aldura85/Mecanum-Autonomous-Vehicle/project_codes/python_pc_folder/Yolo_training_reslut/BoxF1_curve.png

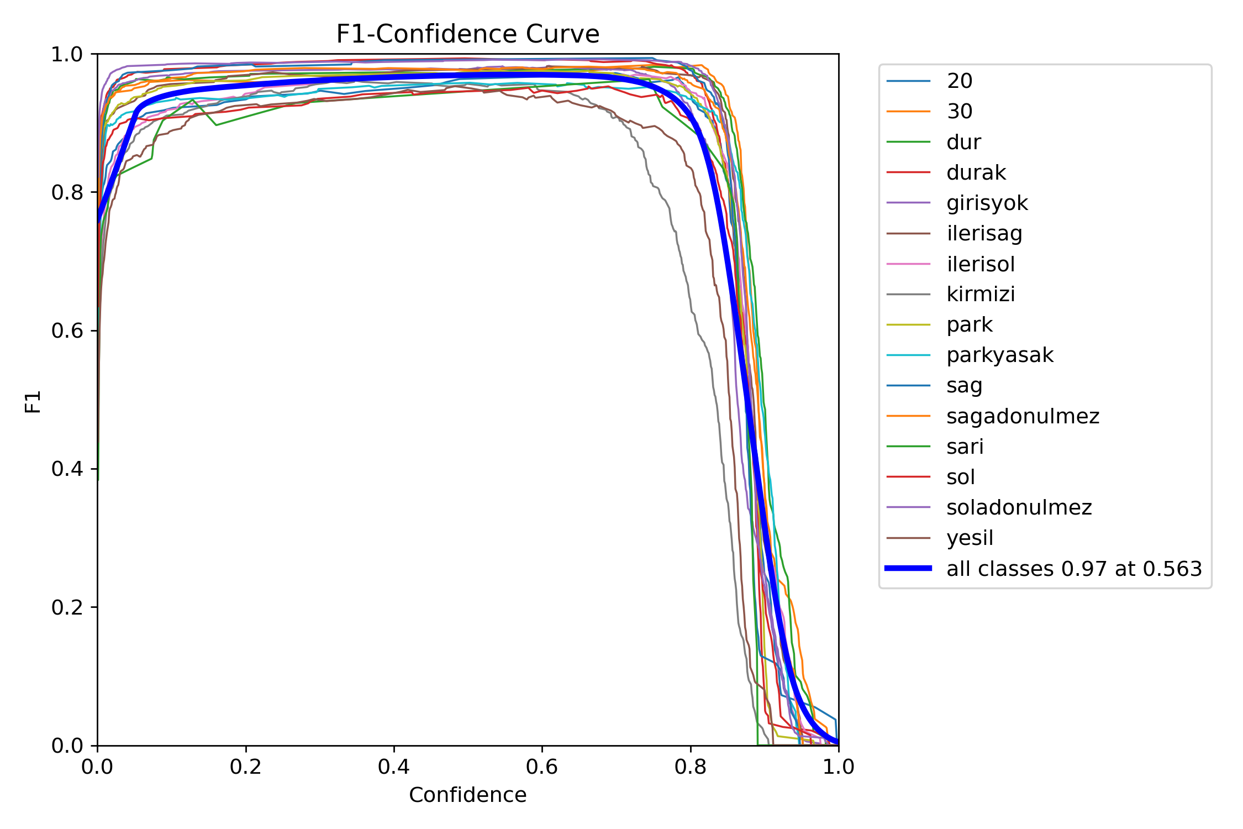
project_codes/python_pc_folder/Yolo_training_reslut/BoxF1_curve.png
