aldura85/Mecanum-Autonomous-Vehicle/project_codes/python_pc_folder/Yolo_training_reslut/confusion_matrix.png

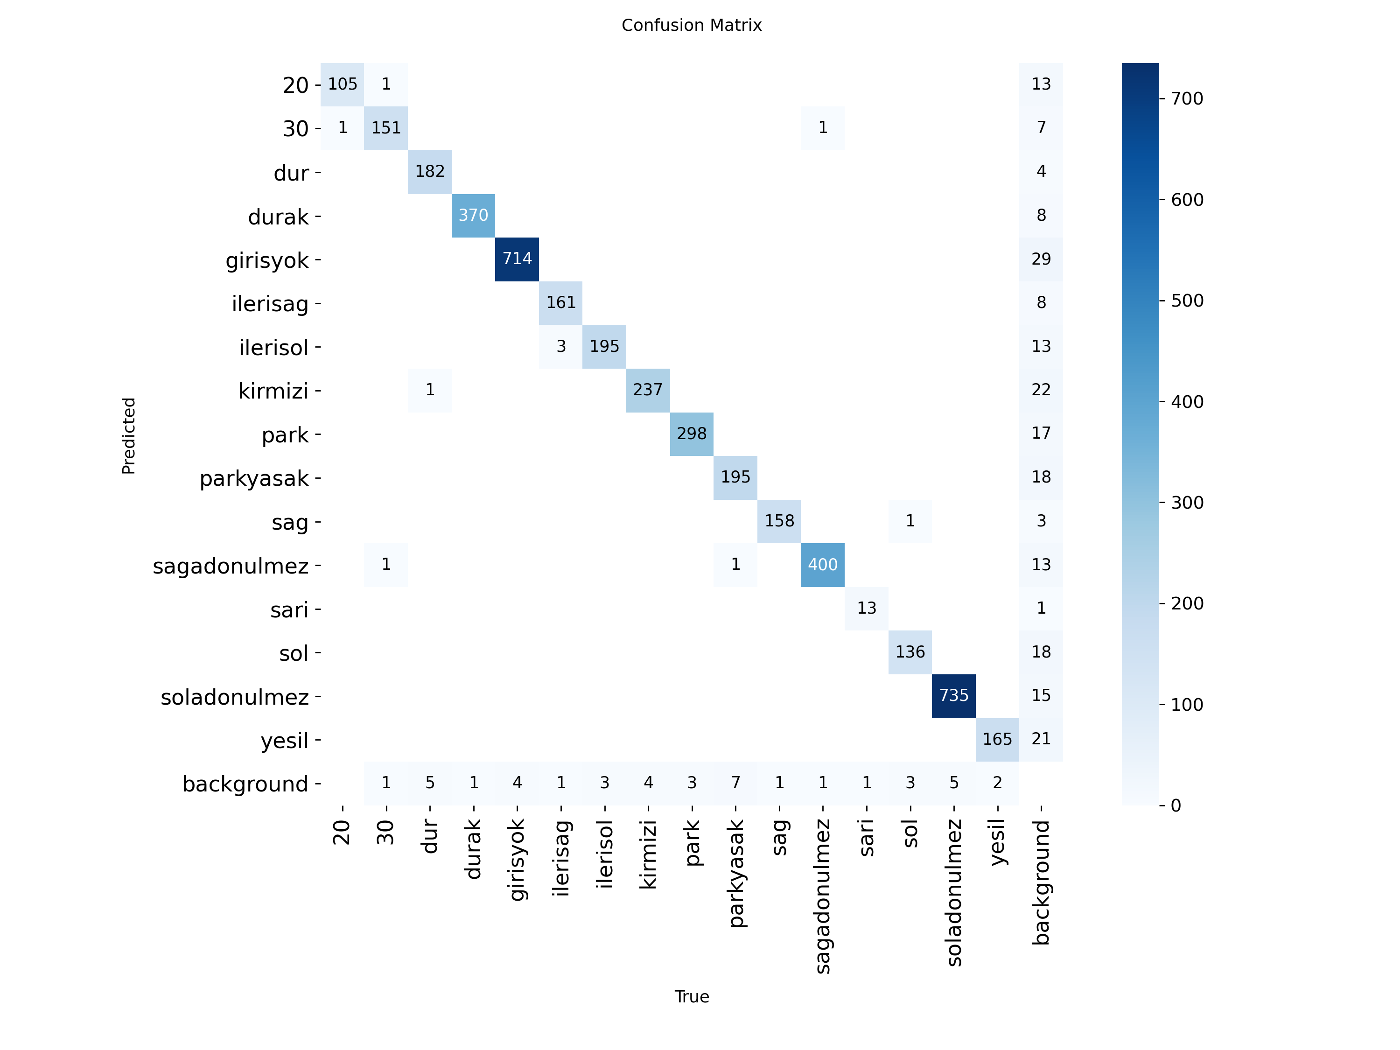
project_codes/python_pc_folder/Yolo_training_reslut/confusion_matrix.png
