aldura85/Mecanum-Autonomous-Vehicle/project_codes/python_pc_folder/Yolo_training_reslut/train_batch2.jpg

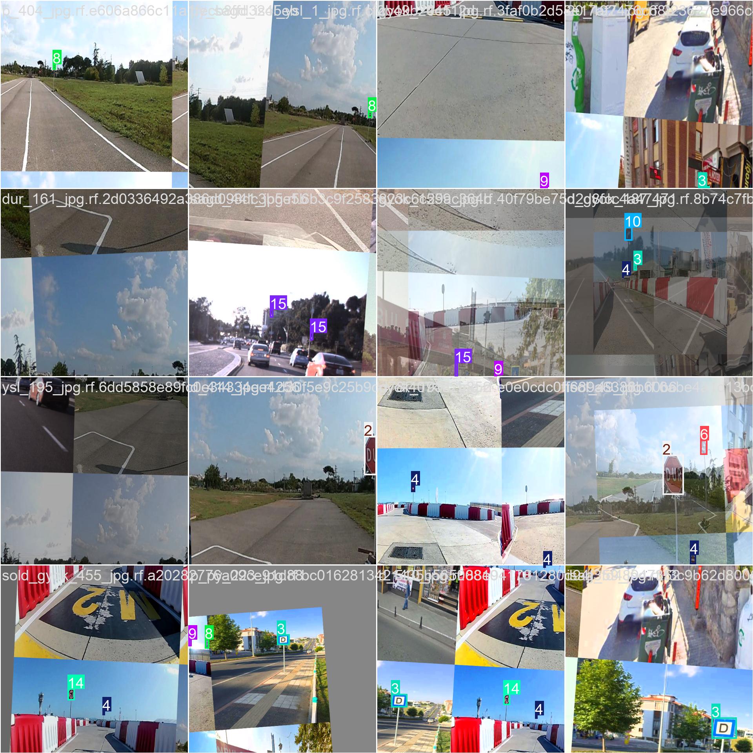
project_codes/python_pc_folder/Yolo_training_reslut/train_batch2.jpg
