aldura85/Mecanum-Autonomous-Vehicle/project_codes/python_pc_folder/Yolo_training_reslut/val_batch1_labels.jpg

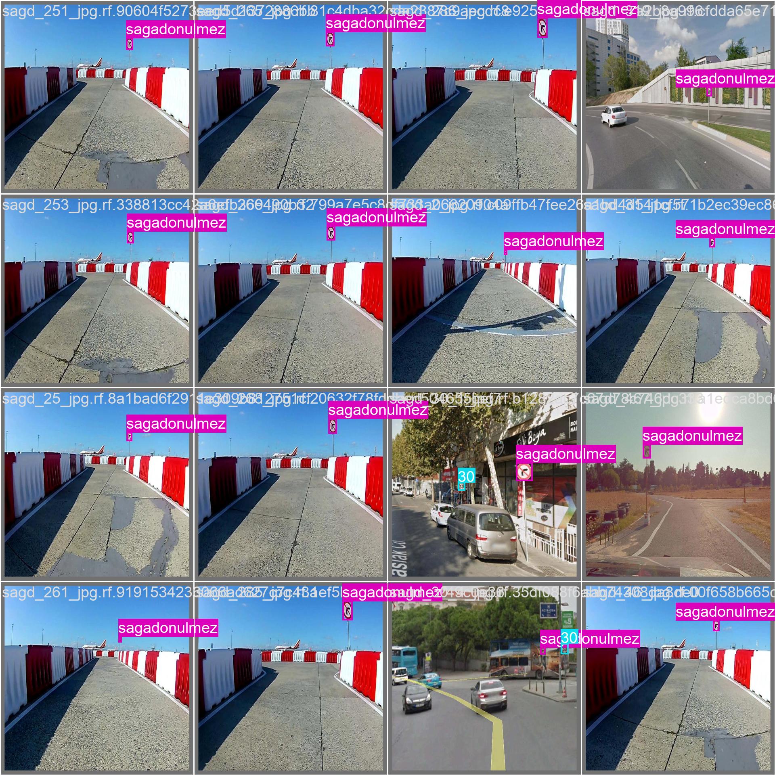
project_codes/python_pc_folder/Yolo_training_reslut/val_batch1_labels.jpg
