aldura85/Mecanum-Autonomous-Vehicle/project_codes/stm_folder/main_car_Core/stm32f407_pic.png

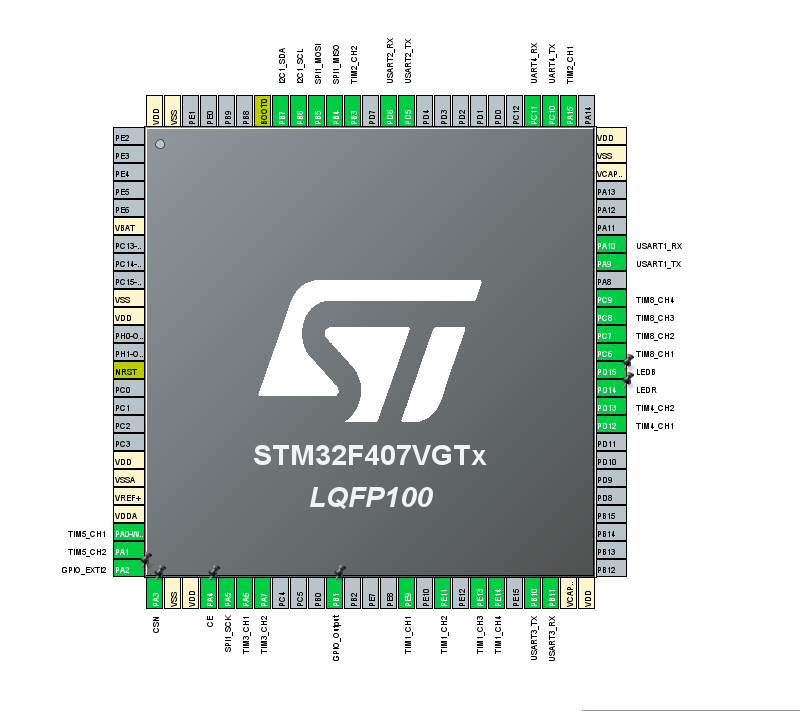
project_codes/stm_folder/main_car_Core/stm32f407_pic.png
