aldura85/Mecanum-Autonomous-Vehicle/project_codes/stm_folder/transmitter_Core/stm32_pic.png

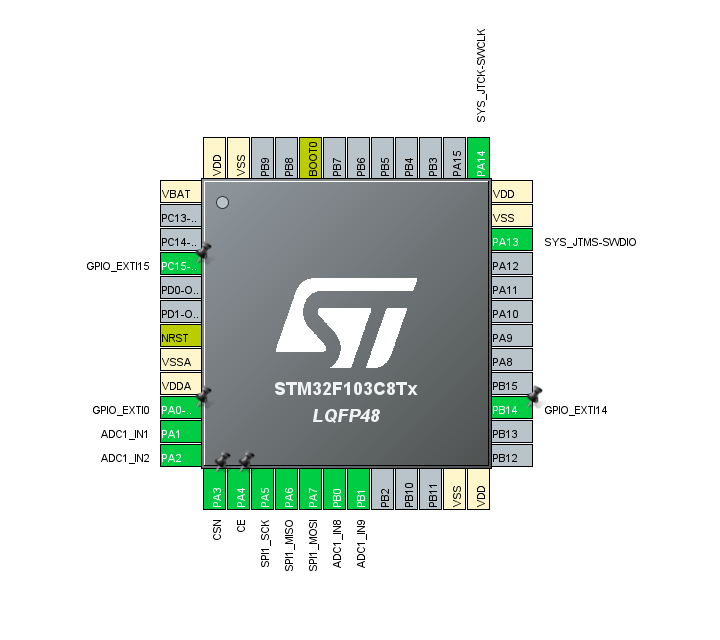
project_codes/stm_folder/transmitter_Core/stm32_pic.png
