aldura85/Mecanum-Autonomous-Vehicle/project_codes/stm_folder/main_car_Core/Inc/main.h

#define CSN_Pin GPIO_PIN_3
#define CSN_GPIO_Port GPIOA
#define CE_Pin GPIO_PIN_4
#define CE_GPIO_Port GPIOA
#define LEDR_Pin GPIO_PIN_14
#define LEDR_GPIO_Port GPIOD
#define LEDB_Pin GPIO_PIN_15
#define LEDB_GPIO_Port GPIOD
